FantasyFactory/SmartThermo/cad/laser.SLDPRT

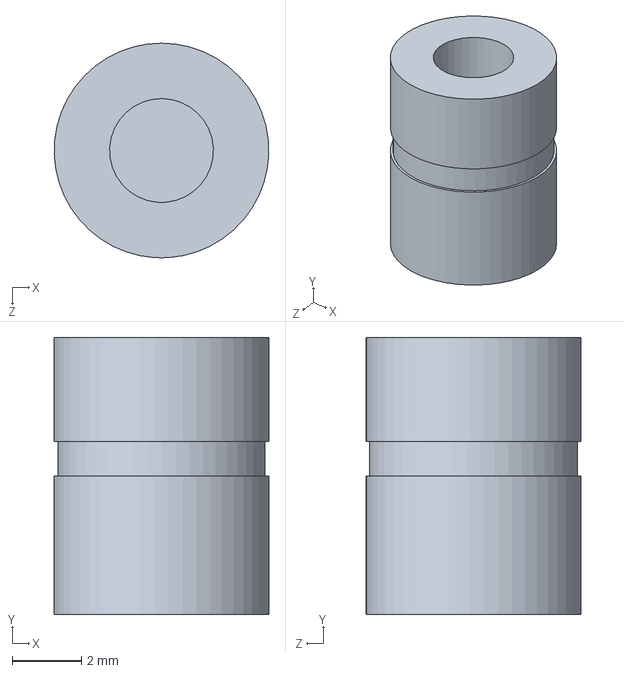
[picture p15: CAD file, 2026-01-16]
cad/laser.SLDPRT
6.20 x 8.00 x 6.20 mm
