FantasyFactory/SmartThermo/cad/Trigger.SLDPRT

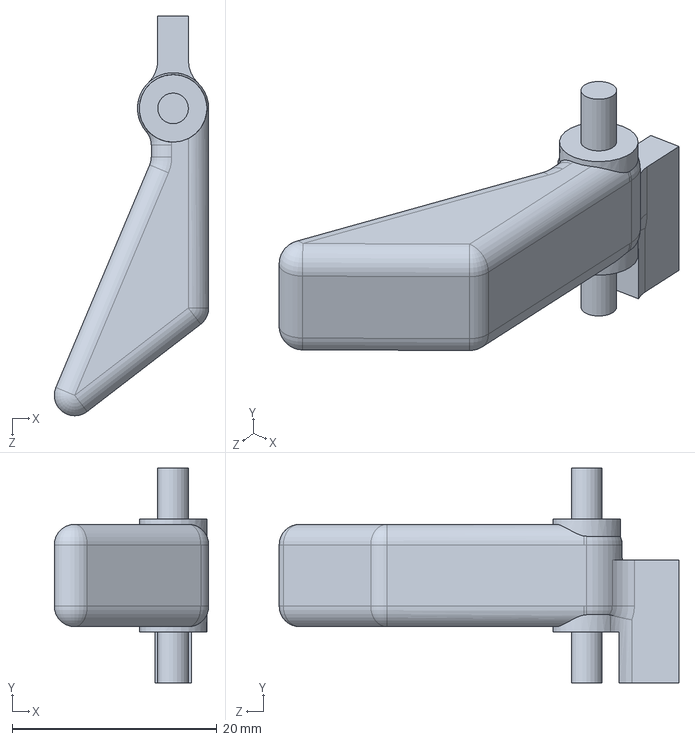
[picture p16: CAD file, 2026-01-16]
cad/Trigger.SLDPRT
15.1 x 21.0 x 39.0 mm
